ammrat13/christmas-ornament-pcb/firmware/ble.py

"""
Module for managing the Bluefruit LE SPI Friend module.

This module provides a way to set up the GATT service on the module, and a way
to update the characteristics of the service. It also provides a way to read
the characteristics.
"""

import adafruit_logging
import platform

logger = adafruit_logging.getLogger()

SERVICE_UUID = b"89-52-25-FE-AC-AF-4F-21-B0-E7-1A-DB-51-E1-16-53"

class BLECharacteristic:
    """
    Each characteristic has the index into the table, as well as a UUID. It also
    has a way to parse values from the module and serialize values for it.
    """

    def __init__(self, index, uuid_bytes, initial_value, wants_reset=True):
        """
        Each characteristic has an index for the Bluefruit LE SPI Friend, as
        well as a UUID for the characteristic itself. An initial value must be
        provided for adding the characteristic for the first time. The
        `want_reset` flag indicates whether the characteristic should be reset
        to its initial value on startup.
        """
        self.index = index
        self.index_bytes = str(index).encode("utf-8")
        self.uuid_bytes = uuid_bytes
        self.initial_value = initial_value
        self.initial_value_bytes = self._serialize(initial_value).encode("utf-8")
        self.wants_reset = wants_reset

    def read(self):
        res = (platform.BLE.command_check_OK(b"AT+GATTCHAR=" + self.index_bytes)
                .decode("utf-8")
                .strip())
        return self._deserialize(res)

    def write(self, value):
        ser = self._serialize(value).encode("utf-8")
        platform.BLE.command_check_OK(b"AT+GATTCHAR=" + self.index_bytes + b"," + ser)

    async def read_async(self):
        res = await platform.BLE.command_async_check_OK(b"AT+GATTCHAR=" + self.index_bytes)
        res = res.decode("utf-8").strip()
        return self._deserialize(res)

    async def write_async(self, value):
        ser = self._serialize(value).encode("utf-8")
        await platform.BLE.command_async_check_OK(b"AT+GATTCHAR=" + self.index_bytes + b"," + ser)

    def add(self):
        """
        Add the characteristic to the service. Different characteristics might
        want to do this in different ways, so this has to be implemented.
        """
        raise NotImplementedError()

    def _serialize(self, value):
        """
        Take the value and return something that can be passed to `AT+GATTCHAR`.
        It should be a `str`, not a `bytes`.
        """
        raise NotImplementedError()

    def _deserialize(self, serialized):
        """
        Take the output of `AT+GATTCHAR` and return the value. It should be a
        `str`, not a `bytes`.
        """
        raise NotImplementedError()

    def _check_index(self, response):
        """
        Check that the response for adding a characteristic returned the index
        we expected.
        """
        return int(response.decode("utf-8").strip()) == self.index

BLE_PROPERTIES_READONLY = b"0x02"
"""Properties for a characteristic that the host can only read."""
BLE_PROPERTIES_WRITEONLY = b"0x0c"
"""
Properties for a characteristic that the host can only write.
"""

class UIntBLECharacteristic(BLECharacteristic):
    """
    A characteristic that represents an unsigned integer. It can have arbitrary
    length, and can be read-only or read-write.
    """

    def __init__(
        self,
        index,
        uuid_bytes,
        properties_bytes=BLE_PROPERTIES_READONLY,
        length=4,
        initial_value=None,
        wants_reset=True,
    ):
        # We use all 1s as a signal to indicate an invalid value
        if initial_value is None:
            initial_value = (1 << (8 * length)) - 1

        super().__init__(index, uuid_bytes, initial_value, wants_reset=wants_reset)
        self.properties_bytes = properties_bytes
        self.length_bytes = str(length).encode("utf-8")

    def _serialize(self, value):
        return hex(value)

    def _deserialize(self, serialized):
        return int(serialized.replace("-", ""), 16)

    def add(self):
        res = platform.BLE.command_check_OK(
            b"AT+GATTADDCHAR=UUID="
            + self.uuid_bytes
            + b",PROPERTIES="
            + self.properties_bytes
            + b",MIN_LEN="
            + self.length_bytes
            + b",MAX_LEN="
            + self.length_bytes
            + b",VALUE="
            + self.initial_value_bytes)
        if not self._check_index(res):
            raise RuntimeError("Wrong index for characteristic.")

# BLE Characteristics
#
# These are the characteristics that we want to expose to the host. They must
# all be registered in the `_characteristics` list below. The Indices must also
# be what the module returns.
#
# There are also "Configuration Characteristics", which have a read-only value
# and a write-only value. The host writes to the write-only value. Each module
# is responsible for reading the value and updating its configuration to reflect
# it. Finally, it should write the new value to the read-only value so that the
# host can read it back. Note that `RD` and `WR` are from the host's
# perspective, meaning we write to the `RD` characteristic and read from the
# `WR` characteristic.

CHAR_HEAP_FREE = UIntBLECharacteristic(1, b"0x0002", length=4)
"""The amount of free heap space on the device, in bytes."""
CHAR_BATTERY_ADC = UIntBLECharacteristic(2, b"0x0003", length=2)
"""The battery voltage as a raw ADC value."""

CHAR_LIGHT_SENSOR_VALUE = UIntBLECharacteristic(3, b"0x0004", length=4)
"""The light sensor value, in millilux."""

CHAR_ACCELEROMETER_COUNT = UIntBLECharacteristic(4, b"0x0005", length=3, initial_value=0)
"""The number of times the accelerometer has activated."""

CHAR_CFG_LIGHT_THRESHOLD_RD = UIntBLECharacteristic(5, b"0x0006", length=4)
"""`CFG_LIGHT_THRESHOLD`, in deci-lux."""
CHAR_CFG_ACCELERATION_THRESHOLD_RD = UIntBLECharacteristic(6, b"0x0007", length=2)
"""`CFG_ACCELERATION_THRESHOLD`, in milli-g."""

CHAR_CFG_LIGHT_THRESHOLD_WR = UIntBLECharacteristic(
    7, b"0x0008", properties_bytes=BLE_PROPERTIES_WRITEONLY, length=4)
"""Paired with `CHAR_CFG_LIGHT_THRESHOLD_RD`."""
CHAR_CFG_ACCELERATION_THRESHOLD_WR = UIntBLECharacteristic(
    8, b"0x0009", properties_bytes=BLE_PROPERTIES_WRITEONLY, length=2)
"""Paired with `CHAR_CFG_ACCELERATION_THRESHOLD_RD`."""

CHAR_BOOT_COUNT = UIntBLECharacteristic(9, b"0x0010", length=1, initial_value=0, wants_reset=False)
"""
The number of times the device has booted. Absolute numbers don't mean much.
But, it's still useful to see if the device is stuck in a boot loop.
"""

_characteristics = [
    CHAR_HEAP_FREE,
    CHAR_BATTERY_ADC,
    CHAR_LIGHT_SENSOR_VALUE,
    CHAR_ACCELEROMETER_COUNT,
    CHAR_CFG_LIGHT_THRESHOLD_RD,
    CHAR_CFG_ACCELERATION_THRESHOLD_RD,
    CHAR_CFG_LIGHT_THRESHOLD_WR,
    CHAR_CFG_ACCELERATION_THRESHOLD_WR,
    CHAR_BOOT_COUNT,
]
"""List of all the characteristics."""

def dump_info():
    """
    Dump the result of `ATI` and `AT+GATTLIST` to the log.
    """

    ati_res = platform.BLE.command_check_OK(b"ATI")
    ati_res = ati_res.decode("utf-8").strip()
    logger.info("Result of ATI:")
    for line in ati_res.split("\n"):
        logger.info(f"    {line}")

    gatt_res = platform.BLE.command_check_OK(b"AT+GATTLIST")
    if gatt_res is None:
        logger.info("No GATT services.")
        return

    gatt_res = gatt_res.decode("utf-8").strip()
    logger.info("Result of AT+GATTLIST:")
    for line in gatt_res.split("\n"):
        logger.info(f"    {line}")


def factory_reset(device_name):
    """
    Reset the module to its "default" state.

    This will repopulate the module with the services and characteristics that
    we define here. The device name is taken as a parameter since it comes from
    the configuration file.
    """

    logger.debug("Resetting the BLE module...")

    # Completely reset the device
    platform.BLE.command_check_OK(b"AT+FACTORYRESET", delay=1.0)
    logger.debug("    factory reset device.")

    # Set the device name
    platform.BLE.command_check_OK(b"AT+GAPDEVNAME=" + device_name.encode("utf-8"))
    platform.BLE.command_check_OK(b"ATZ", delay=1.0)
    logger.debug("    set device name.")

    # Create the service
    platform.BLE.command_check_OK(b"AT+GATTADDSERVICE=UUID128=" + SERVICE_UUID)
    logger.debug("    added service.")

    # Add the characteristics
    for char in _characteristics:
        char.add()
        logger.debug(f"    added characteristic {char.index}.")
    platform.BLE.command_check_OK(b"ATZ", delay=1.0)

def set_initial_values():
    """
    Set all the characteristics to their initial values.
    """
    logger.debug("Setting all characteristics to initial values...")
    for char in _characteristics:
        # Some characteristics might not want to be reset on startup.
        if not char.wants_reset:
            continue
        char.write(char.initial_value)
        logger.debug(f"    set characteristic {char.index} to {char.initial_value}.")
